rmm2908/smartcattoy/raspberry/client_websocket.py

import asyncio
import websockets
import json
import serial
import threading
import time
import random

#Serial Connection to Arduino
ser = serial.Serial('/dev/ttyACM0', baudrate = 9600, timeout = 0.05)
#ser = serial.Serial('COM3', baudrate = 9600, timeout = 0.05)
ser.reset_input_buffer()
global autopilotstatus
autopilotstatus = False
autopilot = None
global tof_distance
tof_distance= ""

def findCommandInString(text):
    if "motor1PW" in text:
        return True
    if "motor1D" in text:
        return True
    if "motor2PW" in text:
        return True
    if "motor2D" in text:
        return True

def autopilotMode():
    print("before going into loop")
    while autopilotstatus:
        #print(autopilotstatus)
        #print("Sending Autopilot command")
        if tof_distance != "" and int(tof_distance) > 150:
            print("Distance bigger than 150 - Path is clear, Moving forward")
            ser.write(("100,0,100,0,\n").encode("UTF-8"))
        else:
            print("Path blocked, turning")
            leftD = round(random.random())
            rightD = round(random.random())
            ser.write(("100," + str(leftD)  + ",100," + str(rightD)  + ",\n").en                                                                                                                                                             code("UTF-8"))
        time.sleep(2)

def updateSensorData():
    print("Before starting sensor Update Loop")
    while autopilotstatus:
        line = ser.readline()
        global tof_distance
        tof_distance = line.decode('utf-8')
        print(tof_distance)

def updateAutopilot(content_obj):
    if content_obj["autopilot"]:
        print("autopilot enabled")
        global autopilotstatus
        autopilotstatus = True
        autopilot = threading.Thread(name="autopilot", target=autopilotMode, arg                                                                                                                                                             s=())
        sensorThread = threading.Thread(name="sensorThread", target=updateSensor                                                                                                                                                             Data, args=())
        autopilot.start()
        sensorThread.start()
    else:
        print("Setting autopilot status to false")
        autopilotstatus = False

def createMotorString(content_obj):
 return str(content_obj["motor1PW"]) + "," + str(content_obj["motor1D"]) + "," +                                                                                                                                                              str(content_obj["motor2PW"]) + "," + str(content_obj["motor2D"]) + "," + "\n"

# create handler for each connection
async def handler():
    uri = "ws://192.168.224.195:3000"
    async with websockets.connect(uri) as websocket:
        await websocket.send("{\"request\": \"message from raspberry\"}")
        done = False
        while not done:
            time.sleep(10/1000)
            message = await websocket.recv()
            print(message)
            if "{" in message:
                positionOfContent = message.index("{")
                jsonContent = message[positionOfContent:]
                content_obj = json.loads(jsonContent)
                print(jsonContent)
                if "autopilot" in message:
                    updateAutopilot(content_obj)

                if not autopilotstatus and findCommandInString(message):
                    serialCommand = createMotorString(content_obj)
                    print("SerialCommand: " + serialCommand)
                    ser.write(str(serialCommand).encode("UTF-8"))

asyncio.run(handler())
